BoujeeEnjinia1701/levelhull/cad/drawings/LVH-DWG-001.png

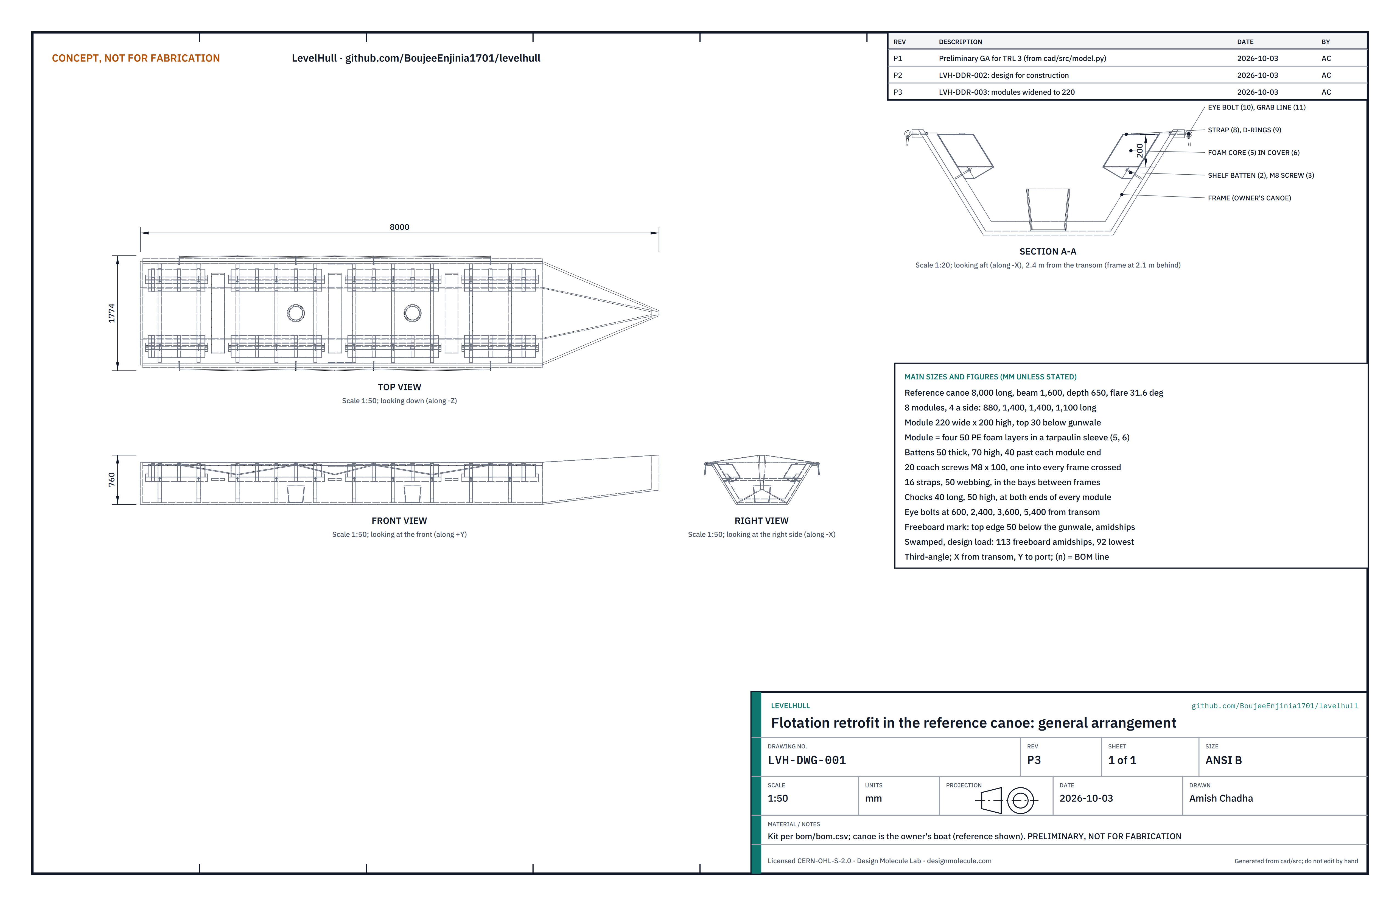
cad/drawings/LVH-DWG-001.png
