BoujeeEnjinia1701/levelhull/media/card.png

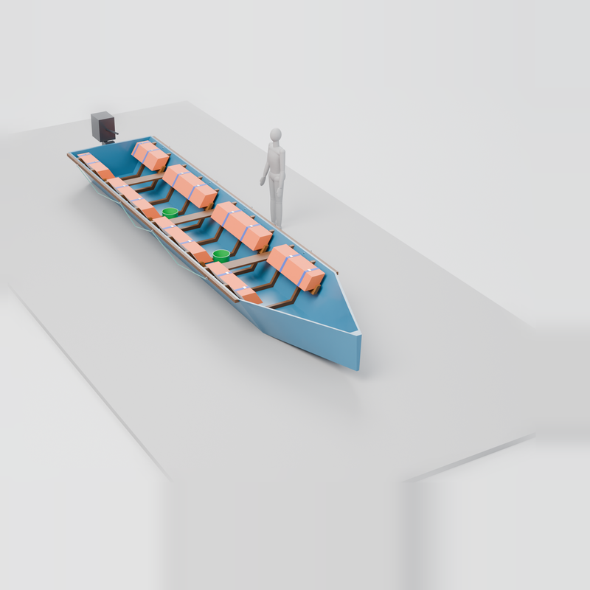
media/card.png
