BoujeeEnjinia1701/levelhull/media/render-detail.png

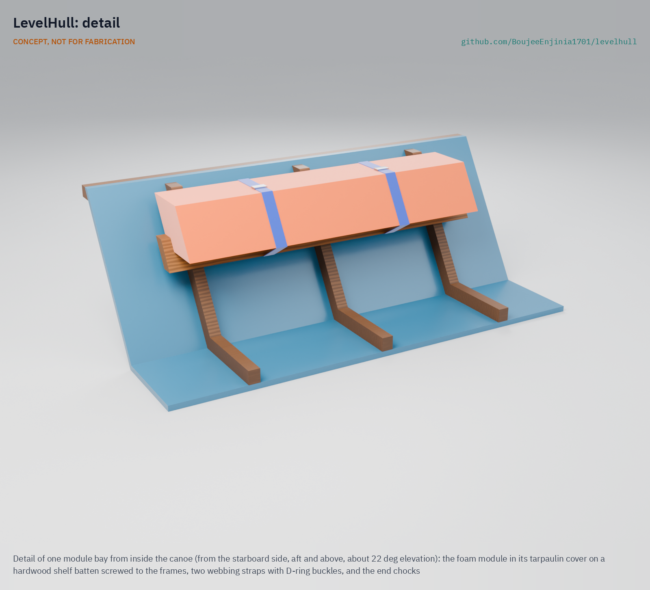
media/render-detail.png
