BoujeeEnjinia1701/levelhull/media/render-exploded.png

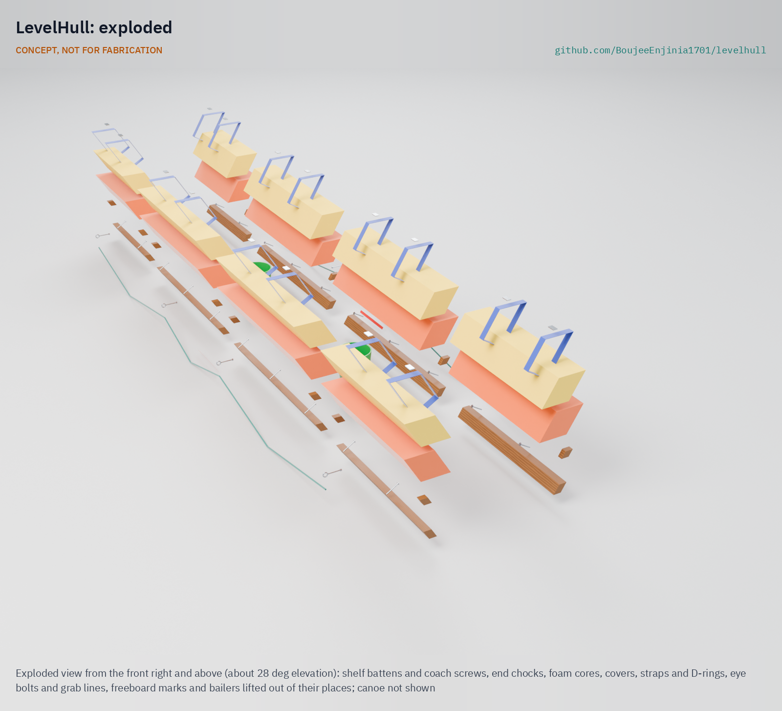
media/render-exploded.png
