BoujeeEnjinia1701/levelhull/media/social-preview.png

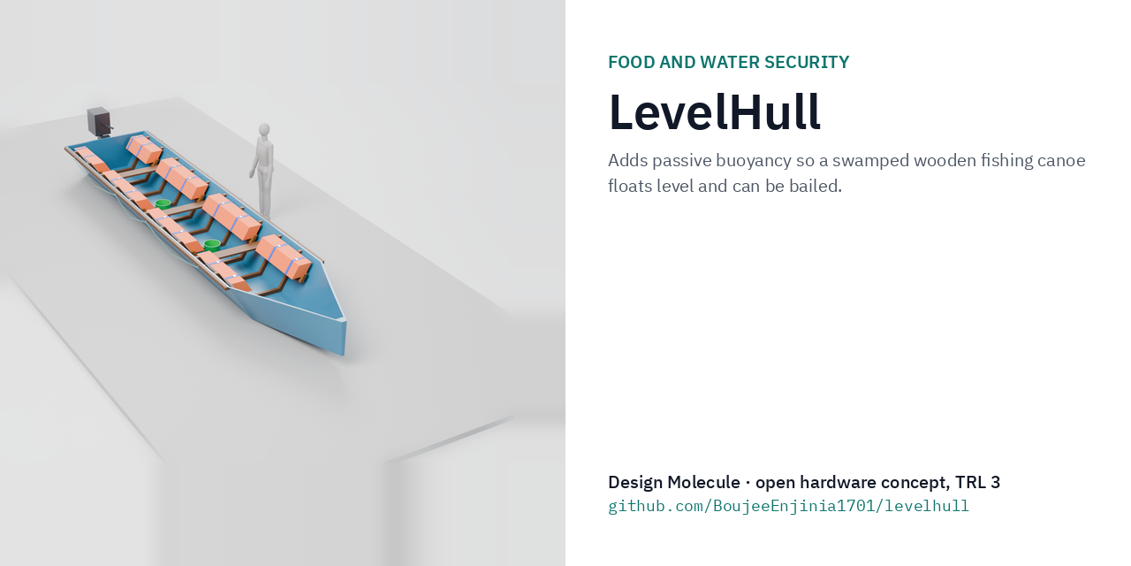
media/social-preview.png
